uwasystemhealth/RAMI/TTGO/LoRaReceiver/LoRaReceiver.ino

//Libraries for LoRa
#include <SPI.h>
#include <LoRa.h>

//define the pins used by the LoRa transceiver module
#define SCK 5
#define MISO 19
#define MOSI 27
#define SS 18
#define RST 14
#define DIO0 26

//433E6 for Asia
//866E6 for Europe
//915E6 for North America
#define BAND 915E6

String LoRaData;

void setup() { 
  //initialize Serial Monitor
  Serial.begin(115200);

  Serial.println("LoRa Receiver Test");
  
  //SPI LoRa pins
  SPI.begin(SCK, MISO, MOSI, SS);
  //setup LoRa transceiver module
  LoRa.setPins(SS, RST, DIO0);
  LoRa.setSpreadingFactor(12);
  LoRa.setSignalBandwidth(31.25E3);
  LoRa.setCodingRate4(8);
  LoRa.setPreambleLength(8);
  LoRa.setSyncWord(0xfa);

  if (!LoRa.begin(BAND)) {
    Serial.println("Starting LoRa failed!");
    while (1);
  }
  Serial.println("LoRa Initializing OK!");
}

void loop() {

  //try to parse packet
  int packetSize = LoRa.parsePacket();
  if (packetSize) {
    //received a packet

    //read packet
    while (LoRa.available()) {
      LoRaData = LoRa.readString();
      Serial.println(LoRaData);
    }
  }
}
